andres-garcia-alves/electronics-power-consumption-meter/Resources/02-building-pcb-01.jpg

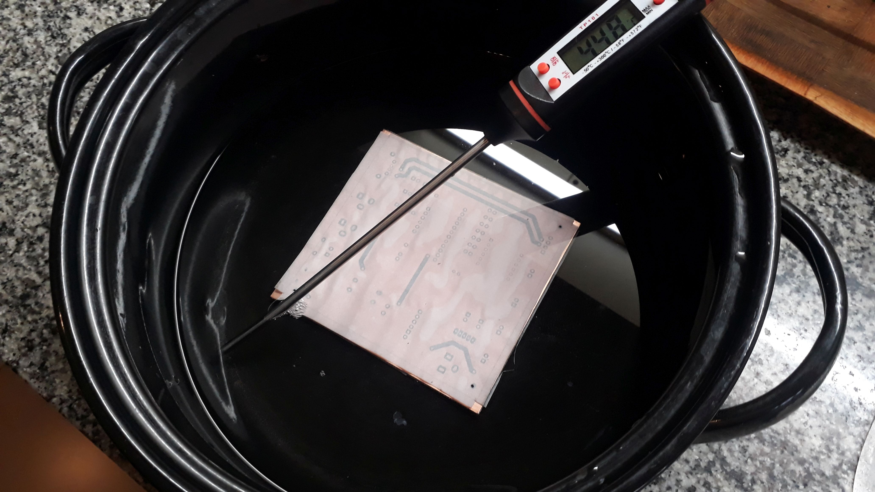
Resources/02-building-pcb-01.jpg
