andres-garcia-alves/electronics-power-consumption-meter/Resources/02-building-pcb-02.jpg

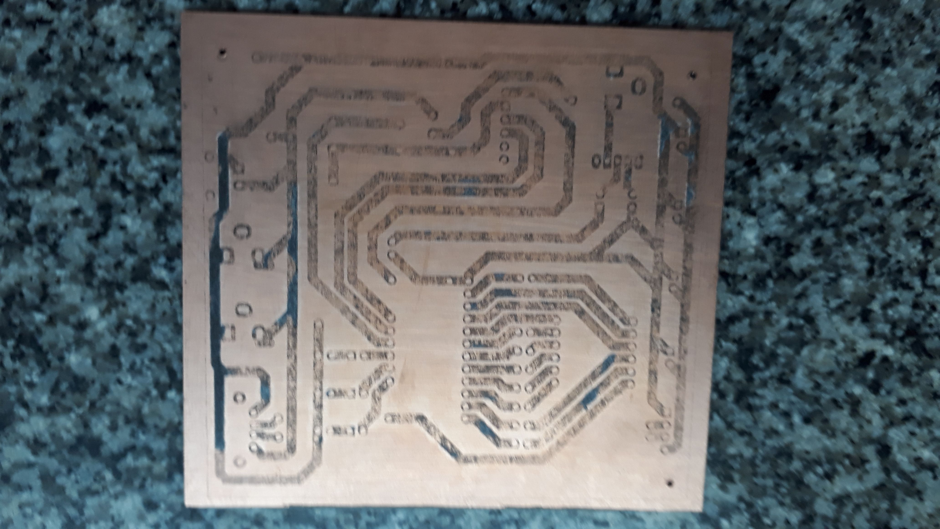
Resources/02-building-pcb-02.jpg
