andres-garcia-alves/electronics-power-consumption-meter/Resources/03-assembly-01.jpg

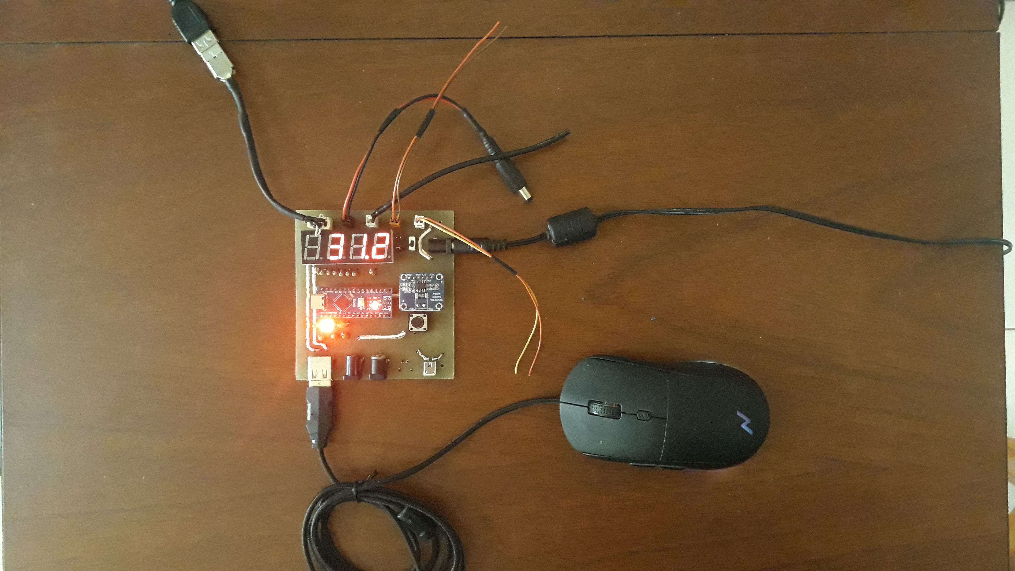
Resources/03-assembly-01.jpg
